engeeknyer/DDSBee/source/cli.h

/*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

 ***************************************************
 *  Nom:	CLI
 *
 *  Autor:	Joan Martínez
 *
 *  Descripcio:   Aquest mòdul implementa les comandes, 
 *             tal com s'han de executar.
 *             (COMMAND LINE INTERFACE)
 ****************************************************/

#ifndef _CLI_
#define _CLI_

/* Defineix la posició on s'emmagatzema 
   el procediment de boot del dispositiu */
#define BOOTVAR_BYTE 511

void cli_init(const uint8_t inici);
int8_t exec_command(const uint8_t * command);

#endif
